UzixLS/rgb2ypbpr/spice/rgb2ypbpr.A.asc

C1: polcap; 22µ; V=16 Irms=0 Rser=11 Lser=0
C2: polcap; 470µ; V=16 Irms=395m Rser=0.2 Lser=0 mfg="Nichicon" pn="UPR1C471MPH" type="Al electrolytic"
D1: diode; 1N4148
Q1: npn; BC547B
Q2: npn; BC547B
Q3: npn; BC547B
Q4: npn; BC547B
Q5: npn; BC547B
Q6: npn; BC547B
Q7: npn; BC547B
R1: res; 1k
R2: res; 500
R3: res; 2k
R4: res; 1k
R5: res; 500
R6: res; 1k
R7: res; 500
R8: res; 500
R9: res; 2k
R10: res; 2k
R11: res; 1k
R12: res; 500
R13: res; 10
R14: res; 15
R15: res; 75
R16: res; 75
R17: res; 1k
R18: res; 10k
R19: res; 500
R20: res; 8k
R21: res; 8k
R22: res; 75
R23: res; 75
V1: voltage; PULSE(1 0 0 1n 1n 4.7m 1)
V3: voltage; PWL file=d2pwl.txt
V4: voltage; PWL file=d1pwl.txt
V6: voltage; PWL file=d0pwl.txt
V7: voltage; 5
Named nets: 0, 5
.tran 20m
